mlab-modules/LION2CELL01/doc/gen/img/LION2CELL01-top.png

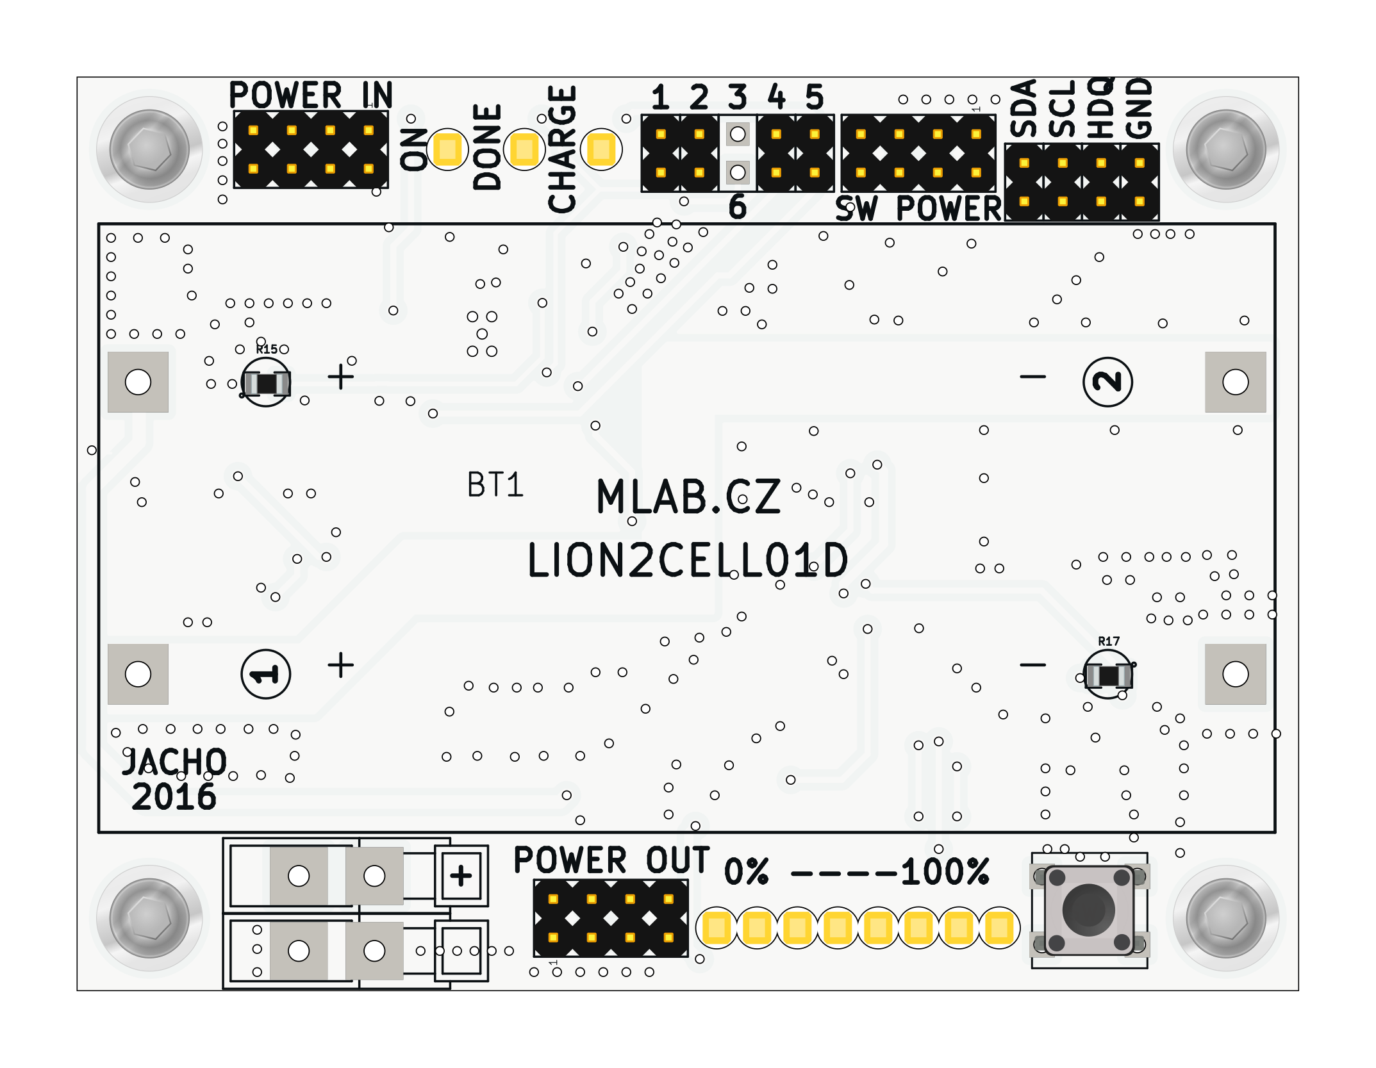
doc/gen/img/LION2CELL01-top.png
